finnff/hyper-osci/docs/research/v3.1-requirements.md

# HYPEROSCI v3.1 - Updated Requirements

**Date:** 2026-01-31  
**Status:** Requirements confirmed

---

## Confirmed Requirements

### 1. Network
- **No venue WiFi** - must provide own
- **Solution:** Dedicated mobile hotspot or portable router
- Recommend: GL.iNet travel router (cheap, reliable, 5GHz support)

### 2. Synchronization
- **±5ms acceptable** ✅
- Software NTP-based sync is sufficient
- No need for hardware trigger (simplifies design)

### 3. Microphone Setup
- **4 separate mics** (one per oscilloscope)
- **CRITICAL: Default/fallback mode required**
  - Must work WITHOUT WiFi/network
  - Must work WITHOUT PC connection
  - Just mic → scope visualization (current setup)
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
