finnff/hyper-osci/hw/carrier/render-bottom.png

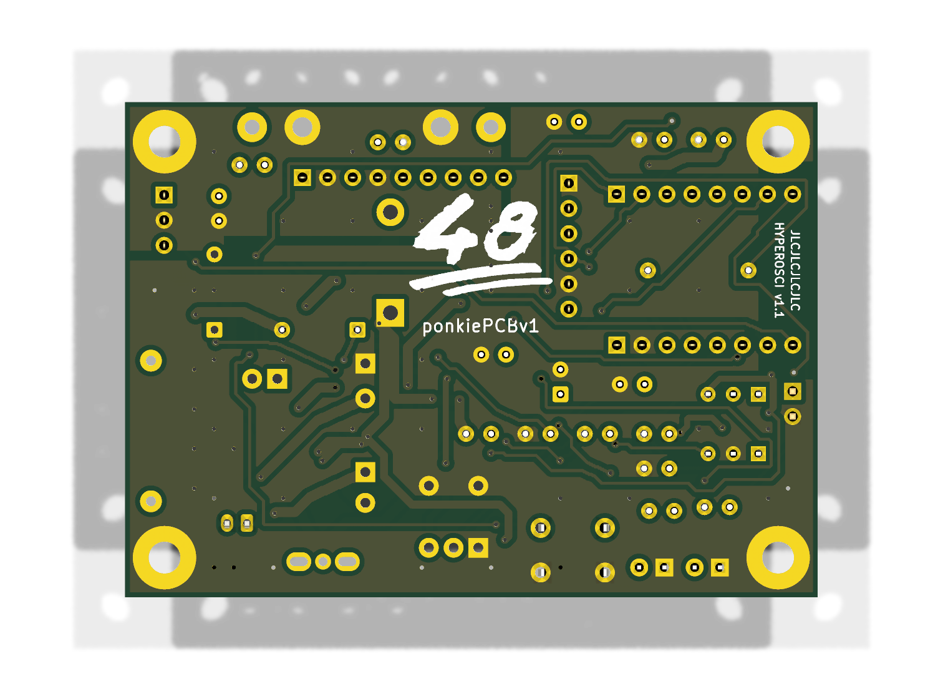
hw/carrier/render-bottom.png
