finnff/hyper-osci/hw/carrier/render-top.png

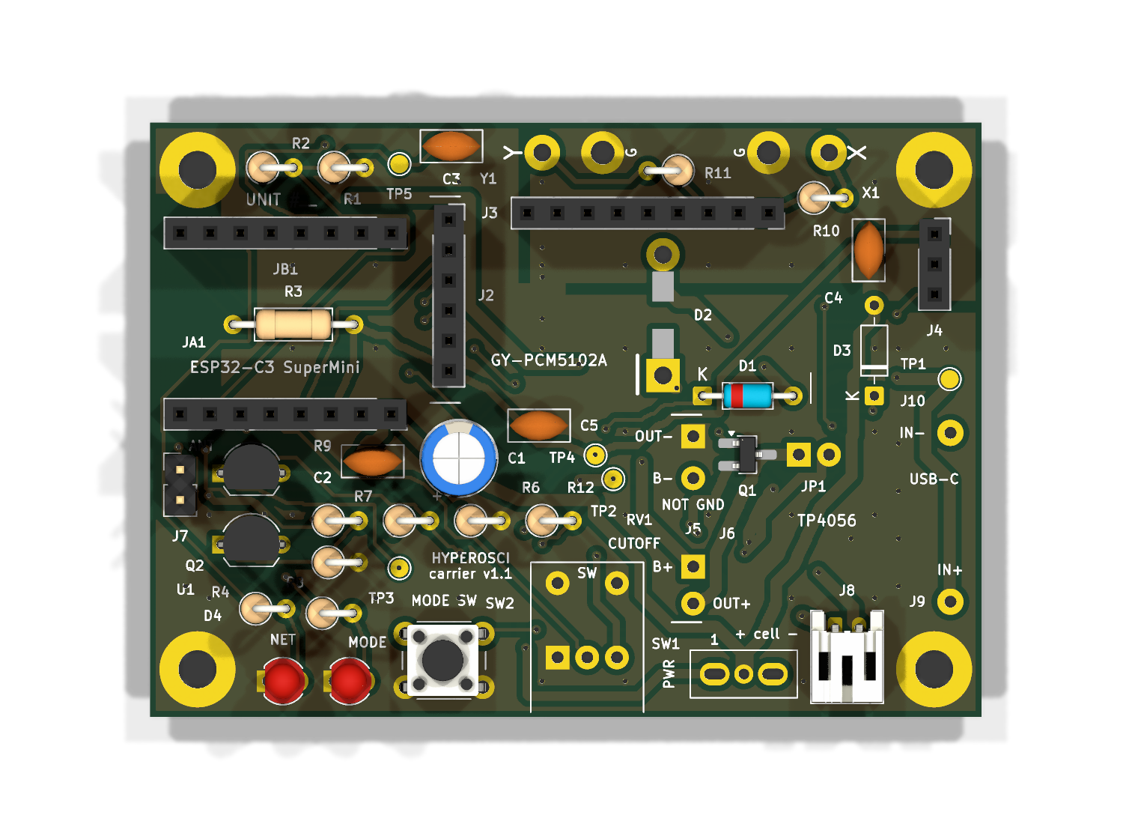
hw/carrier/render-top.png
