finnff/hyper-osci/hw/pin_locs/ESP32C3_overlay.jpg

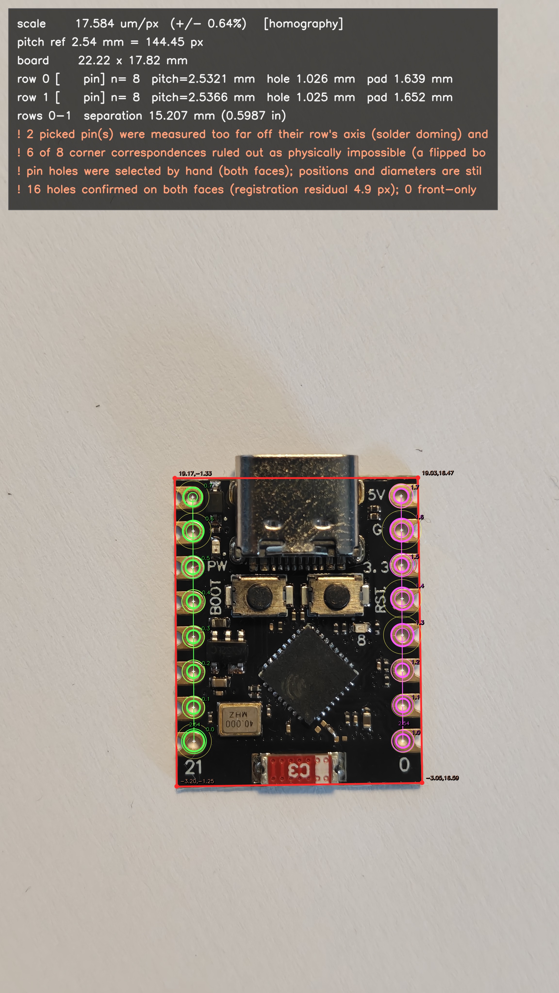
hw/pin_locs/ESP32C3_overlay.jpg
