finnff/hyper-osci/hw/pin_locs/ESP32C3_pads.png

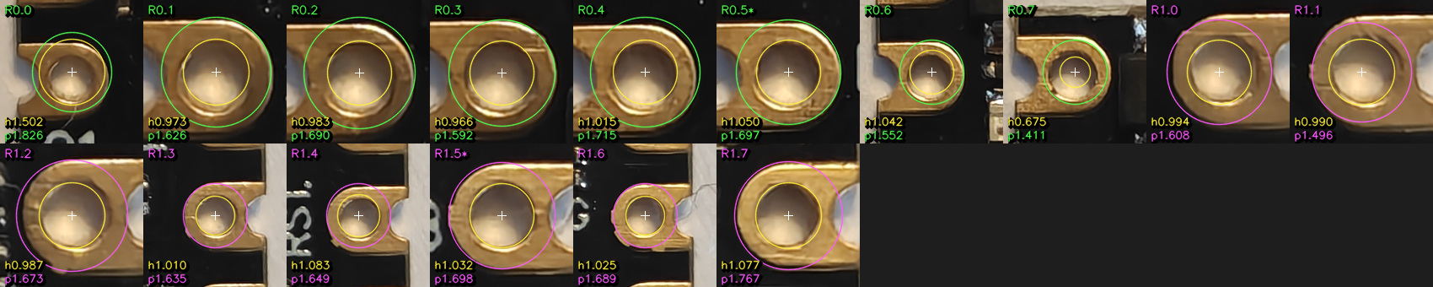
hw/pin_locs/ESP32C3_pads.png
