finnff/hyper-osci/hw/pin_locs/PCM5102A_confirmed.jpg

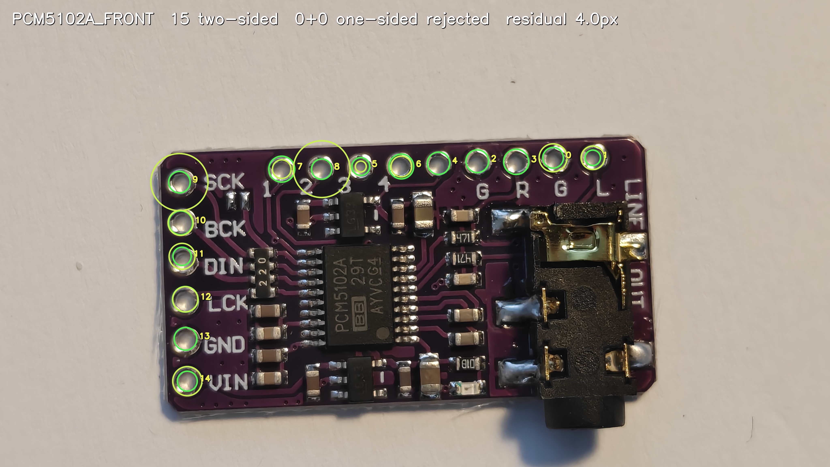
hw/pin_locs/PCM5102A_confirmed.jpg
