finnff/hyper-osci/hw/pin_locs/PCM5102A_overlay.jpg

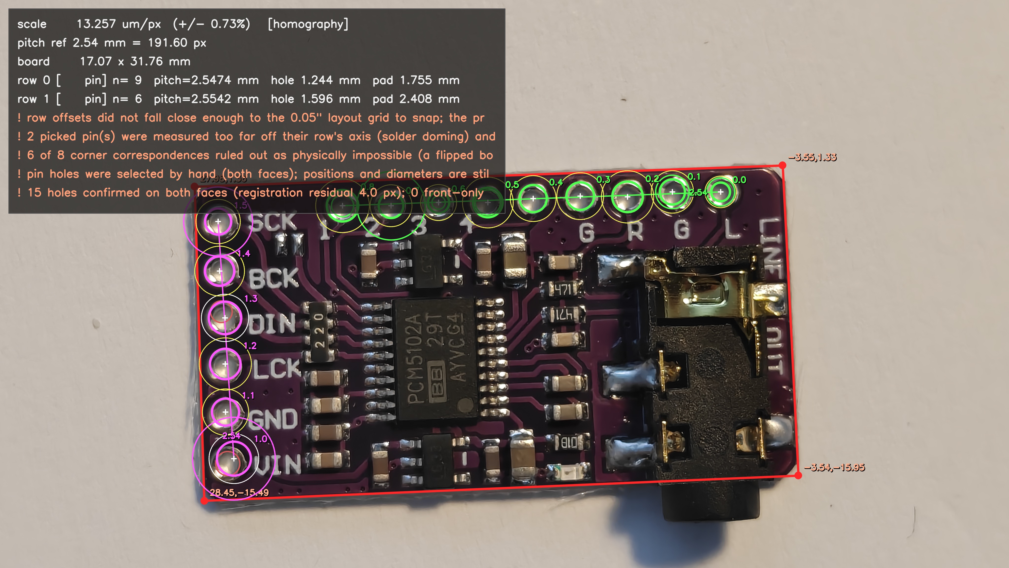
hw/pin_locs/PCM5102A_overlay.jpg
