finnff/hyper-osci/hw/pin_locs/PCM5102A_pads.png

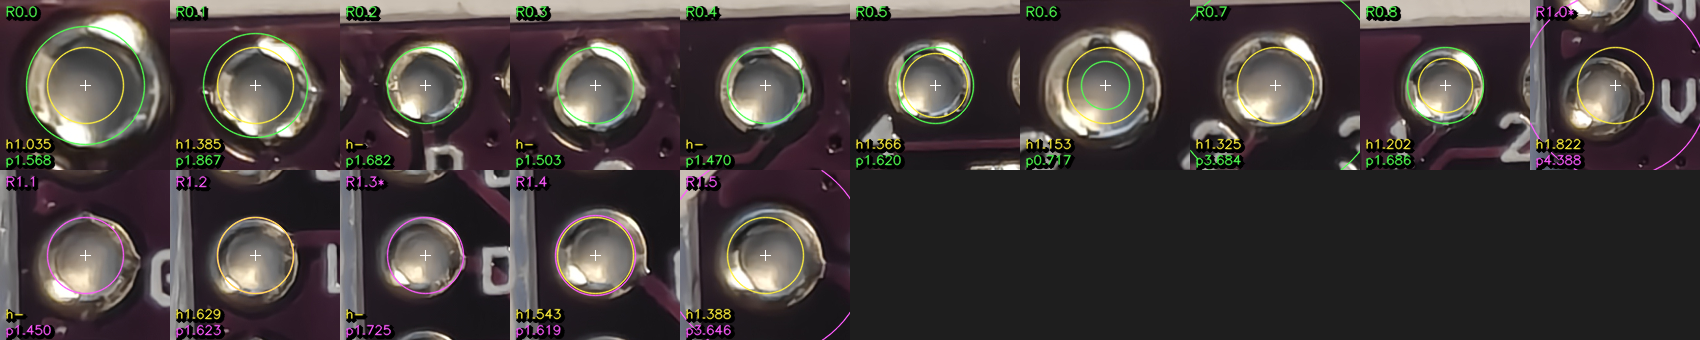
hw/pin_locs/PCM5102A_pads.png
