finnff/hyper-osci/hw/pin_locs/TP4056_confirmed.jpg

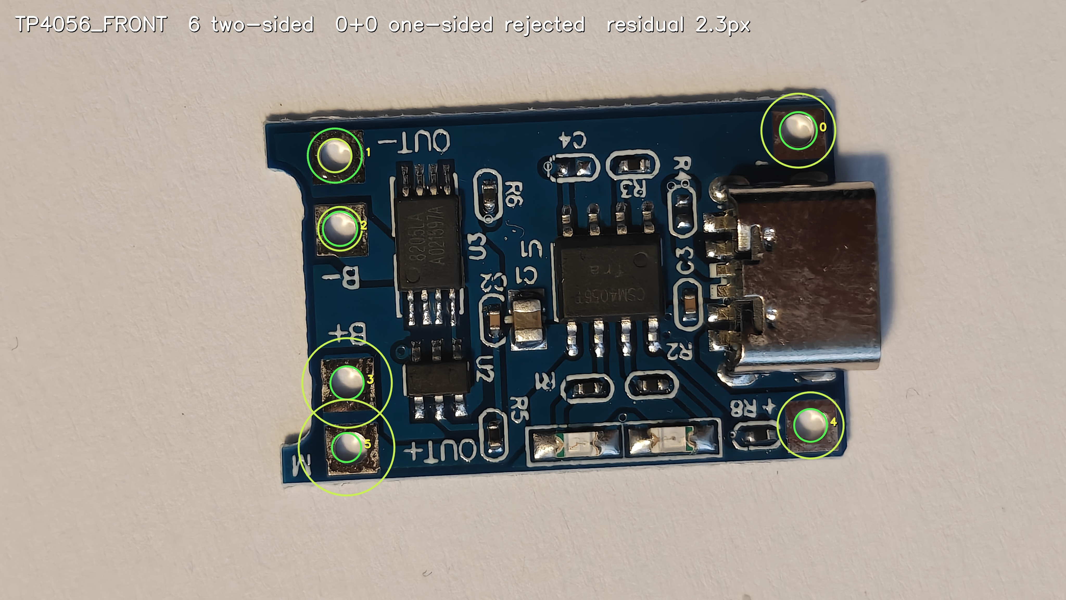
hw/pin_locs/TP4056_confirmed.jpg
