finnff/hyper-osci/hw/pin_locs/TP4056_overlay.jpg

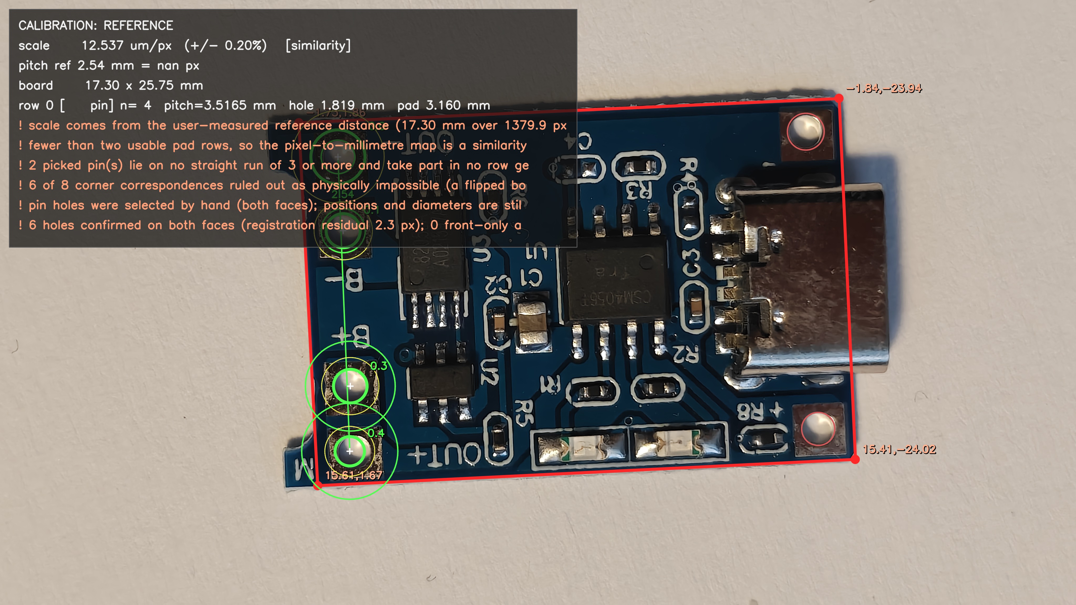
hw/pin_locs/TP4056_overlay.jpg
